StoneRose35/Daddelkiste/PowerControl/system.h

/*
 * system.h
 *
 *  Created on: 06.09.2021
 *      Author: philipp
 */

#ifndef SYSTEM_H_
#define SYSTEM_H_

#define __AVR_ATmega8__
#define F_CPU 1000000L
#define BAT_TH 644
#define I2C_ADDRESS 10


#endif /* SYSTEM_H_ */
